Xinyuan-LilyGO/T-Panel/main/examples/general_test/lvgl_startup_images.h

#pragma once

#include "lvgl.h"

#ifdef __cplusplus
extern "C" {
#endif

extern const lv_image_dsc_t kLvglStartupImage1;
extern const lv_image_dsc_t kLvglStartupImage2;
extern const lv_image_dsc_t kLvglStartupImage3;

#ifdef __cplusplus
}  // extern "C"
#endif
